alf45tar/Pedalino/images/3button.gif

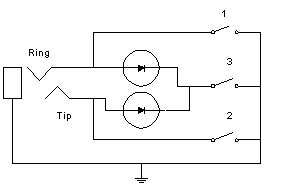
images/3button.gif
