alf45tar/Pedalino/images/ios-interface.png

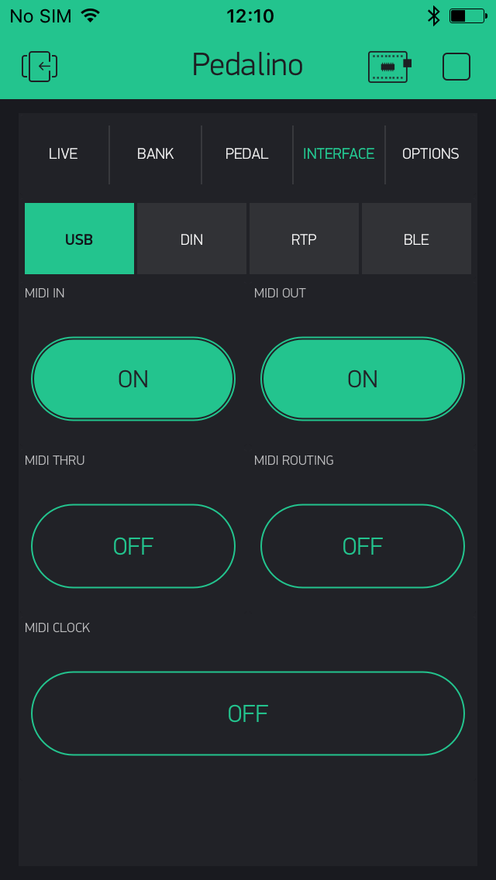
images/ios-interface.png
