alf45tar/Pedalino/images/ladder.png

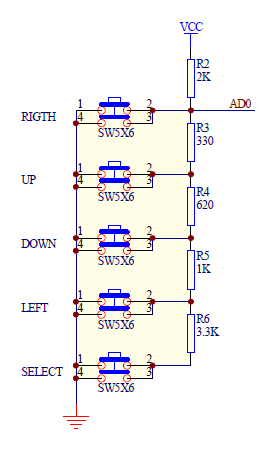
images/ladder.png
