alf45tar/Pedalino/images/PedalinoESP32_bb.png

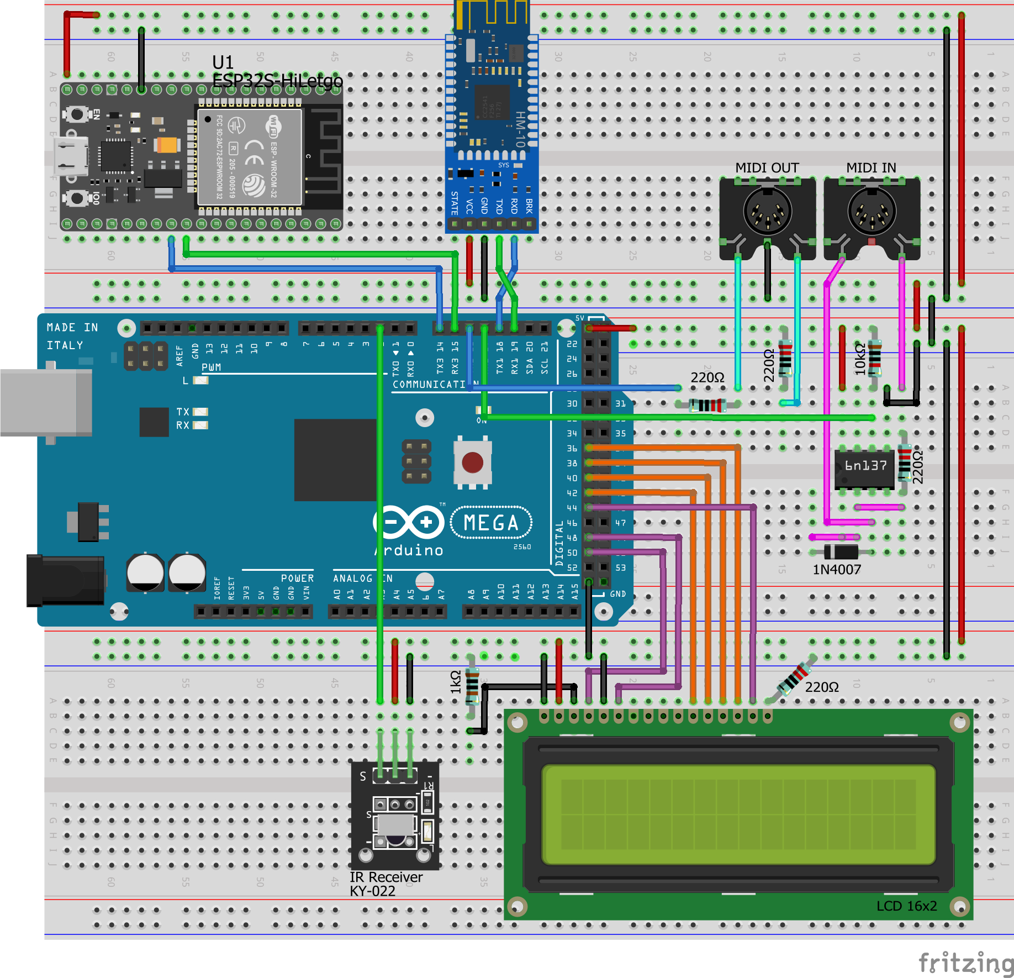
images/PedalinoESP32_bb.png
