alf45tar/Pedalino/images/trs3button.jpg

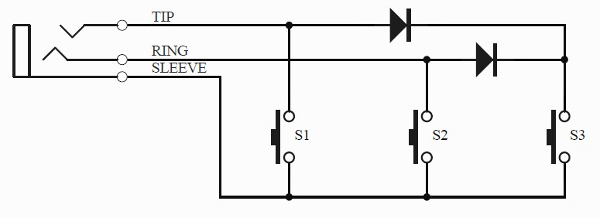
images/trs3button.jpg
